skiselev/flock-v2/images/Flock-V2-3D_Rendering.png

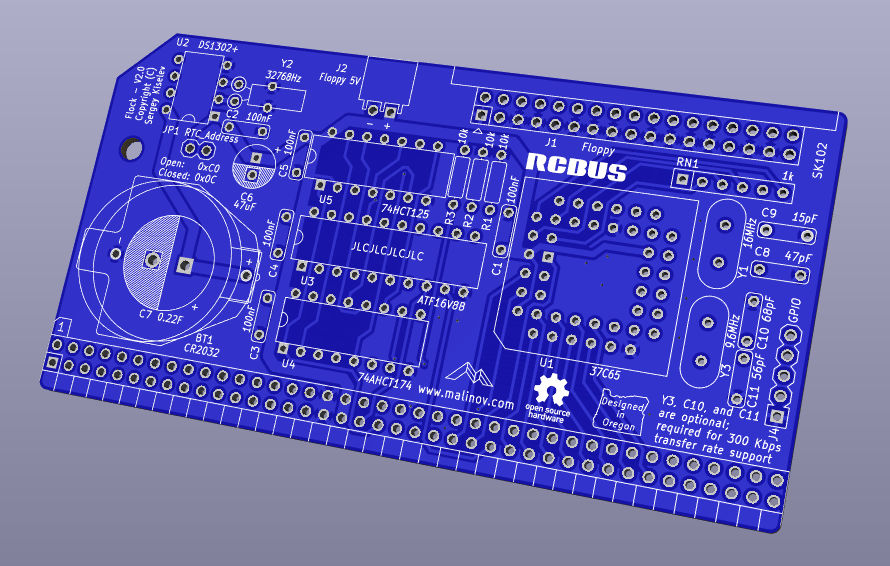
images/Flock-V2-3D_Rendering.png
