skiselev/flock-v2/images/Flock-V2-PCB-Back_Side-800px.jpg

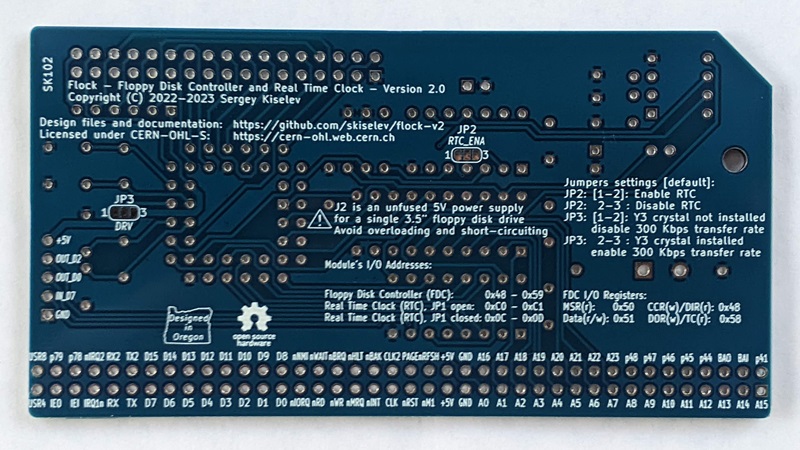
images/Flock-V2-PCB-Back_Side-800px.jpg
