skiselev/flock-v2/images/Flock-V2-Assembled_Board_in_Backplane.jpg

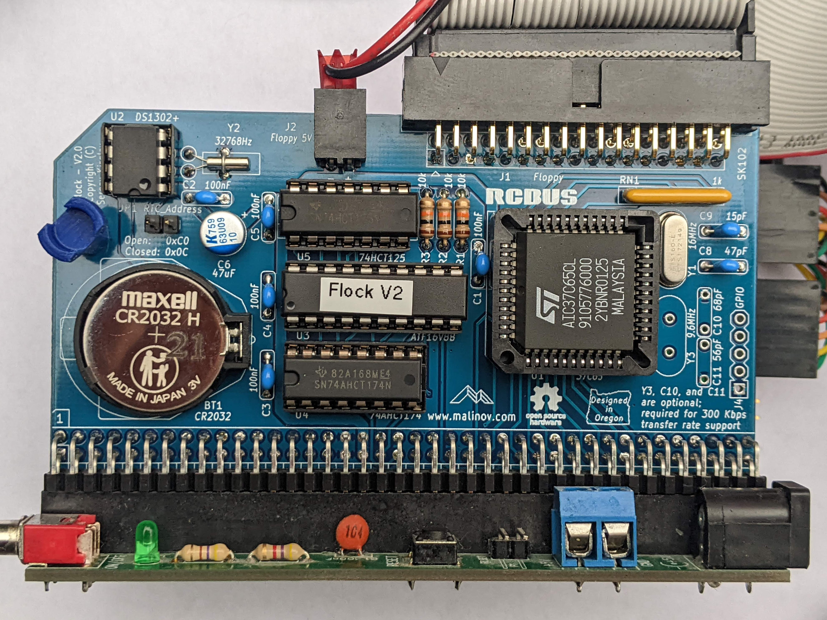
images/Flock-V2-Assembled_Board_in_Backplane.jpg
